TogiFerretFerret/custommic/hardware/kicad/studio-mic.kicad_sch

## KiCad design hardware/kicad/studio-mic.kicad_sch (2026-05-18)

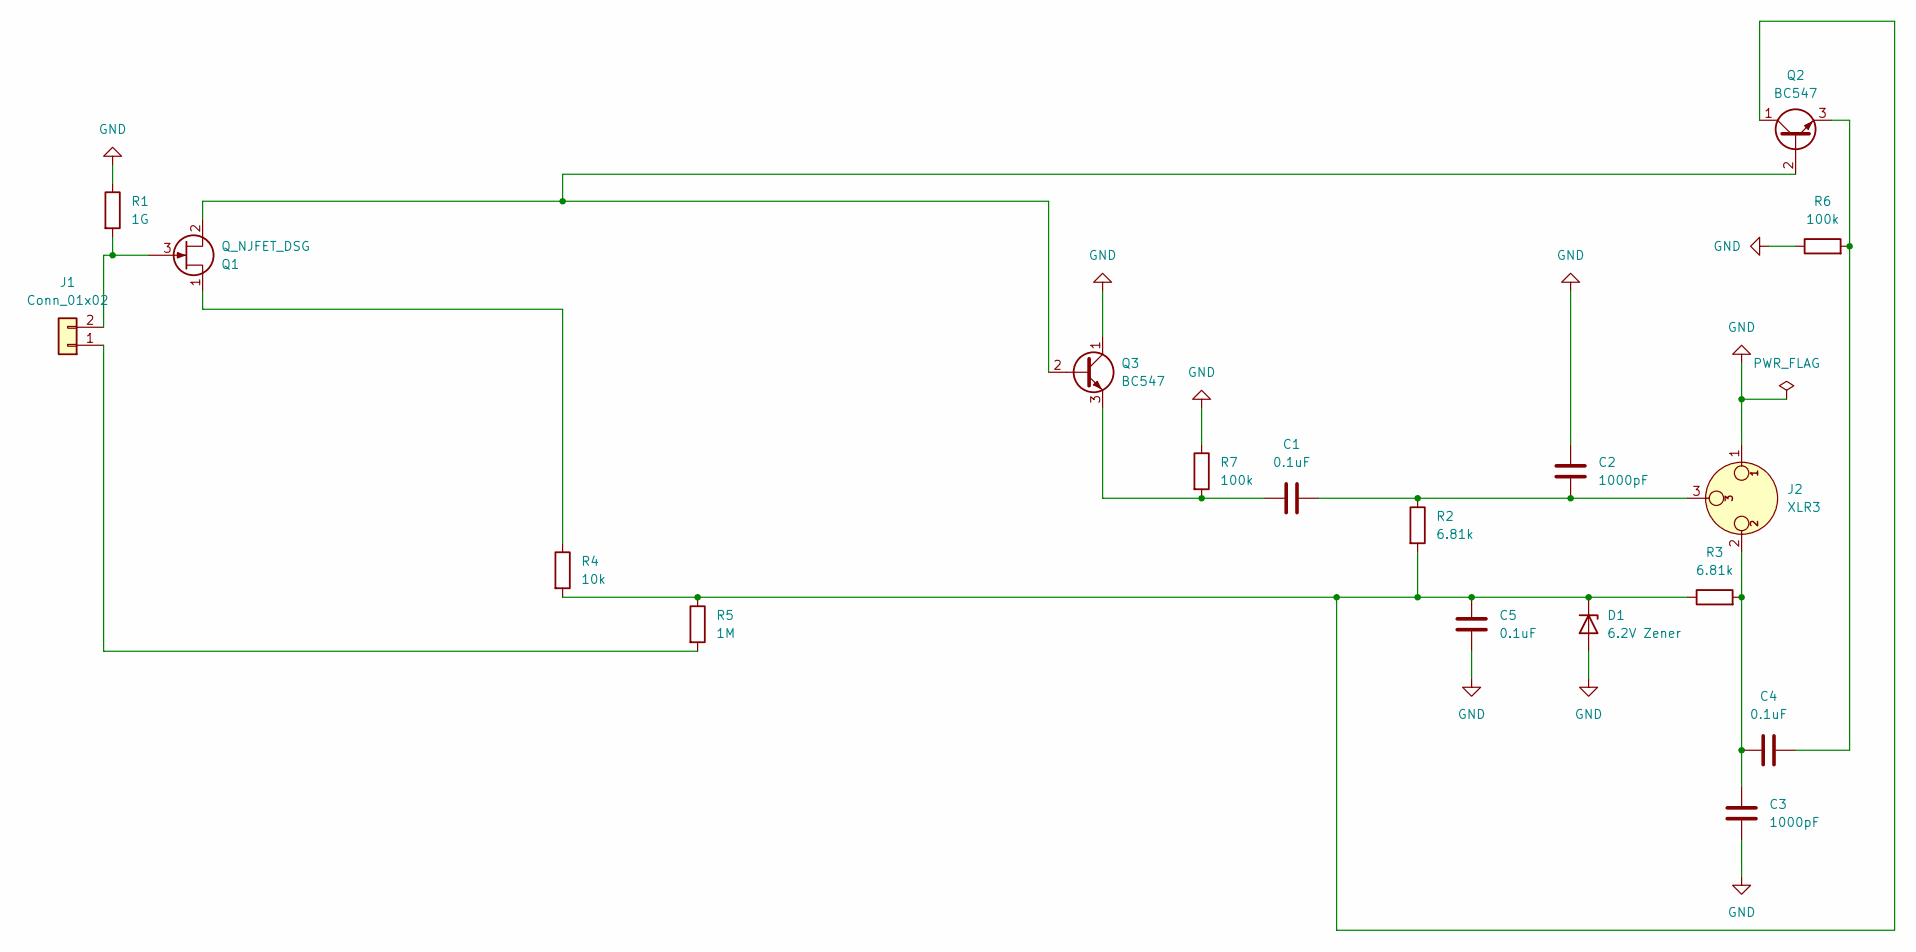
[picture p4: schematic studio-mic.kicad_sch]

Parts:
C1, C4, C5: 0.1uF
C2, C3: 1000pF
D1: 6.2V Zener
J1: Conn_01x02
J2: XLR3
Q1: Q_NJFET_DSG
Q2, Q3: BC547; TO-92_Inline
R1: 1G
R2, R3: 6.81k
R4: 10k
R5: 1M
R6, R7: 100k

Connections:
GND: C2.1, C3.2, C5.2, D1.2 (A), J2.1, Q3.1 (C), R1.1, R6.1, R7.1
unnamed: C1.1, Q3.3 (E), R7.2
unnamed: C1.2, C2.2, J2.3, R2.1
unnamed: C3.1, C4.1, J2.2, R3.2
unnamed: C4.2, Q2.3 (E), R6.2
unnamed: C5.1, D1.1 (K), Q2.1 (C), R2.2, R3.1, R4.2, R5.1
unnamed: J1.1, R5.2
unnamed: J1.2, Q1.3 (G), R1.2
unnamed: Q1.1 (D), R4.1
unnamed: Q1.2 (S), Q2.2 (B), Q3.2 (B)
